andres-garcia-alves/electronics-speaker-upgrade/Resources/01-breadboard-02.jpg

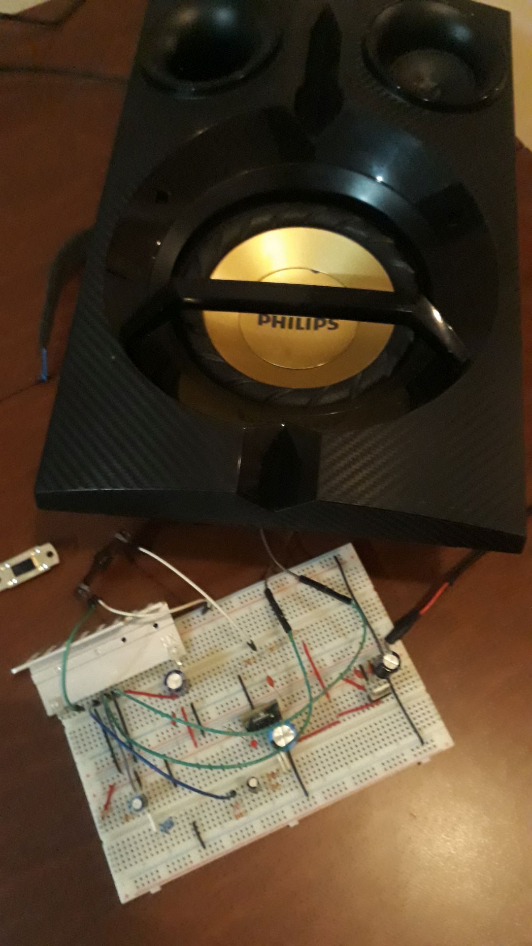
Resources/01-breadboard-02.jpg
